himike12/OLED_Shoe/Hardware/Electronics/nRF52_Reference_Scematics/PCA10040-nRF52832 Bluetooth Smart,ANT,2.4GHz RF Development Board 1_1_1/Production files/GERBER/400150_PCB_Laminate_Specification.pdf

### PCB Laminate Specification

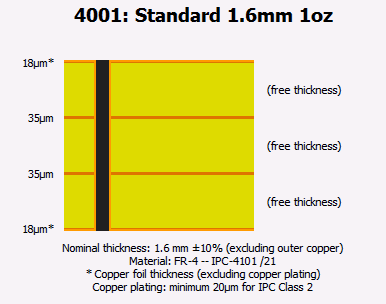
[picture p1: figure]

Page 1 of 1 | Rev. 1.0.0, 2016-03-10

PCB laminate parameters

PCB code | 4000150
Number of copper layers | 4 layers
Laminate material | FR4
Total board thickness | 1.6mm
PCB stackup | See Figure 1
Copper thickness | See Figure 1
Surface finish | Lead-Free HASL
Compliance with environmental directives | RoHS

Table 1: PCB substrate details

The PCB layer stackup order (from top layer and down) shall be as follows with reference to the Gerber file extensions given below:

- Top layer: | .GTL
- Mid layer 1: | .G1
- Mid layer 2: | .G2
- Bottom layer: | .GBL

Stackup

Figure 1: Elprint's standard 4 layer 4001 stackup
