himike12/OLED_Shoe/Hardware/BLE_module/BLE_Serial_Programs/BLE_Serial_Echo/BLE_Serial_Echo.ino

// Copyright (c) Sandeep Mistry. All rights reserved.
// Licensed under the MIT license. See LICENSE file in the project root for full license information.

/*
 * Serial Port over BLE
 * Create UART service compatible with Nordic's *nRF Toolbox* and Adafruit's *Bluefruit LE* iOS/Android apps.
 *
 * BLESerial class implements same protocols as Arduino's built-in Serial class and can be used as it's wireless
 * replacement. Data transfers are routed through a BLE service with TX and RX characteristics. To make the
 * service discoverable all UUIDs are NUS (Nordic UART Service) compatible.
 *
 * Please note that TX and RX characteristics use Notify and WriteWithoutResponse, so there's no guarantee
 * that the data will make it to the other end. However, under normal circumstances and reasonable signal
 * strengths everything works well.
 */


// Import libraries (BLEPeripheral depends on SPI)
#include <SPI.h>
#include <BLEPeripheral.h>
#include "BLESerial.h"

// define pins (varies per shield/board)
#define BLE_REQ   10
#define BLE_RDY   2
#define BLE_RST   9

// create ble serial instance, see pinouts above
BLESerial BLESerial(BLE_REQ, BLE_RDY, BLE_RST);

// LED status
bool LEDState = 0;

void LEDChange();

void setup() {
  // custom services and characteristics can be added as well
  BLESerial.setLocalName("UART");

  Serial.begin(9600);
  BLESerial.begin();

  pinMode(13, OUTPUT);
  digitalWrite(13, HIGH);       // sets the digital pin 13 on
  delay(1000);                  // waits for a second
  digitalWrite(13, LOW);        // sets the digital pin 13 off
}

void loop() {
  BLESerial.poll();

  forward();
  // loopback();
  // spam();
}


// forward received from Serial to BLESerial and vice versa
void forward() {
  if (BLESerial && Serial) {
    int byte;
    while ((byte = BLESerial.read()) > 0) {
      LEDChange(); // Change the state of the LED
      Serial.write((char)byte);
      BLESerial.write((char)byte);
    }
    while ((byte = Serial.read()) > 0) BLESerial.write((char)byte);
  }
}

// echo all received data back
void loopback() {
  if (BLESerial) {
    int byte;
    while ((byte = BLESerial.read()) > 0) BLESerial.write(byte);
  }
}

// periodically sent time stamps
void spam() {
  if (BLESerial) {
    BLESerial.print(millis());
    BLESerial.println(" tick-tacks!");
    delay(1000);
  }
}

// Change the state of the LED
void LEDChange() {
  if(LEDState == 1) {
    LEDState = 0;
    digitalWrite(13, LOW);
  }
  else {
    LEDState = 1;
    digitalWrite(13, HIGH);
  }
}
