himike12/OLED_Shoe/Hardware/BLE_module/Combine_Screen_and_BLE/recieve_data_and_display_modes/imageData.h

// Stores fixed images

#ifndef _IMAGE_DATA_H_
#define _IMAGE_DATA_H_

#include <Arduino.h>

#define SCREEN_HEIGHT 2886
      
//Stores the image
 // 'Gramophone', 312x74px  Brightness = 147
const unsigned char gramophoneLGray [] PROGMEM = {
 0xff, 0xff, 0xf3, 0xff, 0xff, 0xff, 0xff, 0xff, 0xff, 0xff, 0xff, 0xcf, 0xff, 0xff, 0xff, 0x80, 
  0x00, 0x00, 0x00, 0x01, 0xff, 0xff, 0xf8, 0x00, 0x00, 0x00, 0x00, 0x00, 0x00, 0x3f, 0xcc, 0x92, 
  0x00, 0x18, 0x00, 0x3f, 0xff, 0xff, 0xff, 0xff, 0xff, 0xf3, 0xff, 0xff, 0xff, 0xff, 0xff, 0xff, 
  0xff, 0xff, 0xcf, 0xff, 0xff, 0xff, 0x80, 0x00, 0x00, 0x00, 0x01, 0xff, 0xff, 0xf8, 0x00, 0x00, 
  0x00, 0x00, 0x00, 0x00, 0x7f, 0xf9, 0xc0, 0x00, 0x70, 0x00, 0x1f, 0xff, 0xff, 0xff, 0xff, 0xff, 
  0xf3, 0xff, 0xff, 0xff, 0xff, 0xff, 0xff, 0xff, 0xff, 0xcf, 0xff, 0xff, 0xff, 0x80, 0x00, 0x00, 
  0x00, 0x01, 0xff, 0xff, 0xfc, 0x00, 0x00, 0x00, 0x00, 0x00, 0x00, 0x7f, 0xf9, 0x98, 0x00, 0xe2, 
  0x00, 0x1f, 0xff, 0xff, 0xff, 0xff, 0xff, 0xf3, 0xff, 0xff, 0xff, 0xff, 0xff, 0xff, 0xff, 0xff, 
  0x8f, 0xff, 0xff, 0xff, 0x80, 0x00, 0x00, 0x00, 0x03, 0xff, 0xff, 0xfc, 0x00, 0x00, 0x00, 0x00, 
  0x00, 0x00, 0xff, 0xf3, 0xd8, 0x33, 0xc6, 0x00, 0x0f, 0xff, 0xff, 0xff, 0xff, 0xff, 0xe3, 0xff, 
  0xff, 0xff, 0xff, 0xff, 0xff, 0xff, 0xff, 0x9f, 0xff, 0xff, 0xff, 0xc0, 0x00, 0x00, 0x00, 0x03, 
  0xff, 0xff, 0xfc, 0x00, 0x00, 0x00, 0x00, 0x00, 0x00, 0xff, 0xff, 0xd8, 0xe7, 0x1f, 0x00, 0x07, 
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
  0x00, 0x00, 0x00, 0x00, 0x00, 0x00, 0x00, 0x00, 0x00, 0x00, 0x00, 0x00, 0x00, 0x00, 0x00, 0x00, 
  0x00, 0x00, 0x00, 0x00, 0x00, 0x00, 0x00, 0x00, 0x00, 0x00, 0x40, 0x00, 0x00, 0x00, 0x00, 0x00, 
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
};


#endif
