himike12/OLED_Shoe/Hardware/Teensy/Teensy_Screen_Demo/Teensy_Screen_Demo.ino

/* ****************************************************************************************
   Test program for displaying images on the Plastic Logic ePaper displays
**************************************************************************************** */
#include <Adafruit_GFX.h>
#include "PL_microEPD.h"

#define EPD_RST     A4      // Please align with your individual wiring
#define EPD_BUSY    A5      // Please align with your individual wiring
#define EPD_CS      10
PL_microEPD display(EPD_CS, EPD_RST, EPD_BUSY); 


 // 'Avatar1', 148x70px  Brightness = 147
const unsigned char gramophoneLGray [] PROGMEM = {
  0xff, 0xff, 0xff, 0xff, 0xff, 0xff, 0xff, 0xff, 0xff, 0xff, 0xff, 0xff, 0xff, 0xff, 0xff, 0xff, 
  0xf4, 0x00, 0x0f, 0xff, 0xff, 0xff, 0xff, 0xff, 0xff, 0xff, 0xff, 0xff, 0xff, 0xff, 0xff, 0xff, 
  0xff, 0xff, 0xff, 0xf8, 0x00, 0xff, 0xff, 0xff, 0xff, 0xff, 0xff, 0xff, 0xff, 0xff, 0xff, 0xff, 
  0xff, 0xff, 0xff, 0xff, 0xff, 0xff, 0xff, 0x0f, 0xff, 0xff, 0xff, 0xff, 0xff, 0xff, 0xff, 0xff, 
  0xff, 0xff, 0xff, 0xff, 0xff, 0xff, 0xff, 0xff, 0xff, 0xff, 0xff, 0xff, 0xff, 0xff, 0xff, 0xff, 
  0xff, 0xff, 0xff, 0xff, 0xff, 0xff, 0xff, 0xff, 0xff, 0xff, 0xff, 0xff, 0xff, 0xff, 0xff, 0xff, 
  0xff, 0xff, 0xff, 0xff, 0xff, 0xff, 0xff, 0xff, 0xff, 0xff, 0xff, 0xff, 0xff, 0xff, 0xff, 0xff, 
  0xff, 0xff, 0xff, 0xff, 0xff, 0xff, 0xff, 0xff, 0xff, 0xff, 0xff, 0xff, 0xff, 0xff, 0xff, 0xff, 
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
    display.drawBitmap(0, 0, myBitmap, 148, 70, EPD_LGRAY);
    //display.drawBitmap(0, 0, gramophoneDGray, 148, 70, EPD_DGRAY);
    //display.drawBitmap(0, 0, gramophoneBlack, 148, 70, EPD_BLACK);
    // Trigger a full image update
    display.update();
     
    
}

void loop() {

}
