himike12/OLED_Shoe/Hardware/ExampleCode/PlasticLogic_SD_Card_Contents/Reference Source Code/msp430/msp430-spi.c

/*
  Plastic Logic EPD project on MSP430

  Copyright (C) 2013 Plastic Logic Limited

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
  You should have received a copy of the GNU General Public License
  along with this program.  If not, see <http://www.gnu.org/licenses/>.
*/
/*
 * msp430-spi.c -- MSP430 SPI interface driver
 *
 * Authors: Nick Terry <nick.terry@plasticlogic.com>
 *
 */

#include <stdio.h>
#include <stdlib.h>

#include <msp430.h>

#include "types.h"
#include "assert.h"
#include "utils.h"

#include "msp430-defs.h"
#include "msp430-spi.h"
#include "msp430-gpio.h"

#define USCI_UNIT	A
#define USCI_CHAN	0
// Pin definitions for this unit
#define	SPI_SIMO		GPIO(3,4)
#define	SPI_SOMI		GPIO(3,5)
#define	SPI_CLK			GPIO(3,0)
#define SPI_CS GPIO(3,6)

#define SPI_MODE_0 (UCCKPH)                            /* CPOL=0 CPHA=0 */
#define SPI_MODE_1 (0)                         /* CPOL=0 CPHA=1 */
#define SPI_MODE_2 (UCCKPL | UCCKPH)    /* CPOL=1 CPHA=0 */
#define SPI_MODE_3 (UCCKPL)                            /* CPOL=1 CPHA=1 */
#define SPI_MODE_MASK (UCCKPL | UCCKPH)

/* We only support a single SPI bus and that bus is defined at compile
 * time.
 */
int spi_init(u8 spi_channel, u16 divisor)
{
	if (spi_channel != 0)
		return -EACCES;

	UCxnCTL1 |= UCSWRST;					// Put state machine in reset

	// Define chip select pins for multiple controllers
	gpio_request(SPI_SIMO,	PIN_SPECIAL | PIN_OUTPUT);
	gpio_request(SPI_SOMI, 	PIN_SPECIAL | PIN_INPUT);
	gpio_request(SPI_CLK, 	PIN_SPECIAL | PIN_OUTPUT);
	gpio_request(SPI_CS, PIN_GPIO | PIN_OUTPUT);
	//gpio_request(SPI_CS, PIN_GPIO | PIN_OUTPUT | PIN_INIT_HIGH);

	// SPI setting, MSb first, 8bit, Master Mode, 3 pin SPI, Synch Mode
	UCxnCTL0 |= (UCMST | UCSYNC | UCMSB | UCCKPH);

	UCxnCTL1 |= UCSSEL_2;					// SMCLK is selected
    UCxnBR0 = (divisor & 0x00ff);			// f_UCxCLK = 20MHz/1 = 20MHz
    UCxnBR1 = ((divisor >> 8) & 0x00ff);	//
	UCxnIE = 0x00;							// All interrupts disabled

	UCxnCTL1 &= ~UCSWRST;                  	// Release state machine from reset

	return 0;
}

void spi_close(void)
{
	UCxnCTL1 |= UCSWRST;                      // Put state machine in reset
}

u8 spi_write_read_byte(u8 byte)
{
    while (UCxnSTAT & UCBUSY) ;                     // Wait for all TX/RX to finish
    UCxnTXBUF = byte;                        // Write byte
    while (UCxnSTAT & UCBUSY) ;                     // Wait for all TX/RX to finish

    return UCxnRXBUF;                                      // Dummy read to empty RX buffer
}

/*
volatile u8 spi_write_read_byte(u8 byte) --> from Epson code, but not working
{
	unsigned int gie = __get_SR_register() & GIE;	// Store current GIE state

    __disable_interrupt();							// Make this operation atomic

    UCxnIFG &= ~UCRXIFG;							// Ensure RXIFG is clear

        while (!(UCxnIFG & UCTXIFG));				// Wait for TX buff empty
        UCxnTXBUF = 0xff;							// Write dummy byte to generate spi clock
        while (!(UCxnIFG & UCRXIFG));				// Wait for RX buffer (full)
        volatile u8 temp = UCxnRXBUF;						// store the byte

    __bis_SR_register(gie);                         // Restore original GIE state

    return temp;
}
*/

void spi_write_command(u8 command, u8 *params, int count)
{
	int i;

	gpio_set_value_lo(SPI_CS);
	command &= ~0x80;
	spi_write_read_byte(command);
	for (i=0; i<count; i++)
		spi_write_read_byte(*(params+i));
	gpio_set_value_hi(SPI_CS);
}

void spi_write_command_1param(u8 command, u8 param1)
{
	gpio_set_value_lo(SPI_CS);
	command &= ~0x80;
	spi_write_read_byte(command);
	spi_write_read_byte(param1);
	gpio_set_value_hi(SPI_CS);
}

void spi_write_command_2params(u8 command, u8 param1, u8 param2)
{
	gpio_set_value_lo(SPI_CS);
	command &= ~0x80;
	spi_write_read_byte(command);
	spi_write_read_byte(param1);
	spi_write_read_byte(param2);
	gpio_set_value_hi(SPI_CS);
}

void spi_write_command_3params(u8 command, u8 param1, u8 param2, u8 param3)
{
	gpio_set_value_lo(SPI_CS);
	command &= ~0x80;
	spi_write_read_byte(command);
	spi_write_read_byte(param1);
	spi_write_read_byte(param2);
	spi_write_read_byte(param3);
	gpio_set_value_hi(SPI_CS);
}

void spi_write_command_4params(u8 command, u8 param1, u8 param2, u8 param3, u8 param4)
{
	gpio_set_value_lo(SPI_CS);
	command &= ~0x80;
	spi_write_read_byte(command);
	spi_write_read_byte(param1);
	spi_write_read_byte(param2);
	spi_write_read_byte(param3);
	spi_write_read_byte(param4);
	gpio_set_value_hi(SPI_CS);
}

u8 spi_read_command_1param(u8 command)
{
	gpio_set_value_lo(SPI_CS);
	command |= 0x80;
	spi_write_read_byte(command);
	u8 temp = spi_write_read_byte(0x00);
	gpio_set_value_hi(SPI_CS);
	return temp;
}

u8* spi_read_command_2params(u8 command)
{
	static u8 return_value[2];
	gpio_set_value_lo(SPI_CS);
	command |= 0x80;
	spi_write_read_byte(command);
	return_value[0] = spi_write_read_byte(0x00);
	return_value[1] = spi_write_read_byte(0x00);
	gpio_set_value_hi(SPI_CS);
	return return_value;
}

void spi_read_command_2params1(u8 command, u8 *return_value)
{
	gpio_set_value_lo(SPI_CS);
	command |= 0x80;
	spi_write_read_byte(command);
	*return_value = spi_write_read_byte(0x00);
	*(return_value+1) = spi_write_read_byte(0x00);
	gpio_set_value_hi(SPI_CS);
}

int spi_read_command(u8 command, u8 *read_values_p, int count)
{
	int i;

	gpio_set_value_lo(SPI_CS);
	command |= 0x80;
	spi_write_read_byte(command);
	for (i=0; i<count; i++)
		*(read_values_p+i) = spi_write_read_byte(0x00);
	gpio_set_value_hi(SPI_CS);

	return i;
}

void print_spi_read_command(u8 command, int count)
{
	u8 *read_values_p;
	int i, ret;

	read_values_p = (u8*) malloc(count * sizeof(u8));
	if (read_values_p==0)
		abort_now("Fatal error in msp430-spi.c - print_spi_read_command: malloc not successful", ABORT_MISC);

	ret = spi_read_command(command, read_values_p, count);

	printf("Reg[%02xh] = ", command);
	for(i=0; i<ret; i++)
		printf("0x%02x ", *(read_values_p+i));
	printf("\n");

	free(read_values_p);
}

u8* spi_read_command_3params(u8 command)
{
	static u8 return_value[3];
	gpio_set_value_lo(SPI_CS);
	command |= 0x80;
	spi_write_read_byte(command);
	return_value[0] = spi_write_read_byte(0x00);
	return_value[1] = spi_write_read_byte(0x00);
	return_value[2] = spi_write_read_byte(0x00);
	gpio_set_value_hi(SPI_CS);
	return return_value;
}

u8* spi_read_command_4params(u8 command)
{
	static u8 return_value[4];
	gpio_set_value_lo(SPI_CS);
	command |= 0x80;
	spi_write_read_byte(command);
	return_value[0] = spi_write_read_byte(0x00);
	return_value[1] = spi_write_read_byte(0x00);
	return_value[2] = spi_write_read_byte(0x00);
	return_value[3] = spi_write_read_byte(0x00);
	gpio_set_value_hi(SPI_CS);
	return return_value;
}

u8 spi_read_command_1param_1dummy(u8 command)
{
	gpio_set_value_lo(SPI_CS);
	command |= 0x80;
	spi_write_read_byte(command);
	spi_write_read_byte(command); //dummy
	u8 temp = spi_write_read_byte(0x00);
	gpio_set_value_hi(SPI_CS);
	return temp;
}

void spi_write_command_and_bulk_data(u8 command, u8 *buffer, size_t size)
{
	gpio_set_value_lo(SPI_CS);
	command &= ~0x80;
	spi_write_read_byte(command);

    while (size--) {
    	spi_write_read_byte(*buffer);
    	buffer++;
    }
	gpio_set_value_hi(SPI_CS);
}

void spi_read_command_and_bulk_data(u8 command, u8 *buffer, size_t size)
{
	gpio_set_value_lo(SPI_CS);
	command |= 0x80;
	spi_write_read_byte(command);

    while (size--)
    {
    	*buffer = spi_write_read_byte(0x00); // 0x00 is dummy data
    	buffer++;
    }
	gpio_set_value_hi(SPI_CS);
}
/*
void spi_write_bulk_data(u8 *buffer, size_t size)
{
    while (size--) {
    	spi_write_byte(*buffer++, 1);
    }
}
*/

void spi_write_command_byte_repeat(u8 command, u8 data, size_t size)
{
	gpio_set_value_lo(SPI_CS);
	command &= ~0x80;
	spi_write_read_byte(command);

	while (size--) {
    	spi_write_read_byte(data);
    }
	gpio_set_value_hi(SPI_CS);
}
