himike12/OLED_Shoe/Hardware/ExampleCode/PlasticLogic_SD_Card_Contents/Reference Source Code/waveform.c

/*
 * waveform.h
 *
 *  Created on: 05.09.2014
 *      Author: andreas.meier
 */

#ifndef WAVEFORM_H_
#define WAVEFORM_H_

#include "waveform.h"
#include "types.h"
#include "UC8156.h"

u8 waveform_debug[WAVEFORM_LENGTH]= { \
0xAA, 0x6A, 0xAA, 0xAA, \
0x22, 0x22, 0x22, 0x22, \
0x00, 0x00, 0x00, 0x00, \
0x11, 0x11, 0x11, 0x11, \
0x11, 0x11, 0x11, 0x11, \
0x11, 0x11, 0x11, 0x11, \
0x11, 0x11, 0x11, 0x11, \
0x11, 0x11, 0x11, 0x11, \
0x11, 0x11, 0x11, 0x11, \
0x11, 0x11, 0x11, 0x11, \
0x11, 0x11, 0x11, 0x11, \
0x11, 0x11, 0x11, 0x11, \
0x11, 0x11, 0x11, 0x11, \
0x11, 0x11, 0x11, 0x11, \
0x11, 0x11, 0x11, 0x11, \
0x11, 0x11, 0x11, 0x11, \
0x11, 0x11, 0x11, 0x11, \
0x11, 0x11, 0x11, 0x11, \
0x11, 0x11, 0x11, 0x11, \
0x11, 0x11, 0x11, 0x11, \
0x11, 0x11, 0x11, 0x11, \
0x11, 0x11, 0x11, 0x11, \
0x11, 0x11, 0x11, 0x11, \
0x11, 0x11, 0x11, 0x11, \
0xF1, \
0x01, \
0x01, \
0x01, \
0x01, \
0x01, \
0x01, \
0x01, \
0x01, \
0x01, \
0x01, \
0x01, \
0x01, \
0x01, \
0x01, \
0x01, \
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
};

u8 waveform_long_null[WAVEFORM_LENGTH] = { \
                0xAA, 0xAA, 0xAA, 0xAA, \
                0xAA, 0xAA, 0xAA, 0xAA, \
                0xAA, 0xAA, 0xAA, 0xAA, \
                0xAA, 0xAA, 0xAA, 0xAA, \
                0xAA, 0xAA, 0xAA, 0xAA, \
                0xAA, 0xAA, 0xAA, 0xAA, \
                0xAA, 0xAA, 0xAA, 0xAA, \
                0xAA, 0xAA, 0xAA, 0xAA, \
                0xAA, 0xAA, 0xAA, 0xAA, \
                0xAA, 0xAA, 0xAA, 0xAA, \
                0xAA, 0xAA, 0xAA, 0xAA, \
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
0x00, 0x00, 0x00, 0x00,\
0x00, 0x00, 0x00, 0x00,\
0x00, 0x00, 0x00, 0x00,\
0x00, 0x00, 0x00, 0x00,\
0x00, 0x00, 0x00, 0x00,\
0x00, 0x00, 0x00, 0x00,\
0x00, 0x00, 0x00, 0x00,\
0x41,\
0x41,\
0x41,\
0x11,\
0x00,\
0x00,\
0x00,\
0x00,\
0x00,\
0x00,\
0x00,\
0x00,\
0x00,\
0x00,\
0x00,\
0x00,\
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
};

u8 waveform_S011_V1_0_VJW003_V2_T23_WfId3_uc8156_lut[] = { \
0x28, 0x6A, 0x6A, 0x69, \
0x28, 0xAA, 0x6A, 0x69, \
0x28, 0x2A, 0x68, 0x69, \
0x28, 0x2A, 0x29, 0x69, \
0x2A, 0x28, 0x29, 0xA9, \
0x29, 0x29, 0x29, 0x29, \
0xAA, 0xAA, 0xAA, 0xAA, \
0x00, 0x00, 0x00, 0x00, \
0x00, 0x00, 0x00, 0x00, \
0x00, 0x00, 0x00, 0x00, \
0x00, 0x00, 0x00, 0x00, \
0x00, 0x00, 0x00, 0x00, \
0x00, 0x00, 0x00, 0x00, \
0x00, 0x00, 0x00, 0x00, \
0x00, 0x00, 0x00, 0x00, \
0x00, 0x00, 0x00, 0x00, \
0x00, 0x00, 0x00, 0x00, \
0x00, 0x00, 0x00, 0x00, \
0x00, 0x00, 0x00, 0x00, \
0x00, 0x00, 0x00, 0x00, \
0x00, 0x00, 0x00, 0x00, \
0x00, 0x00, 0x00, 0x00, \
0x00, 0x00, 0x00, 0x00, \
0x00, 0x00, 0x00, 0x00, \
0x21, 0x11, 0x11, 0x11, \
0x11, 0x61, 0x21, 0x00, \
0x00, 0x00, 0x00, 0x00, \
0x00, 0x00, 0x00, 0x00, \
0x00, 0x00, 0x00, 0x00, \
0x00, 0x00, 0x00, 0x00, \
};

/*
 u8 waveform_MTP_array[] = { \
};
 */

#endif /* WAVEFORM_H_ */
