himike12/OLED_Shoe/Hardware/BLE_module/Screen_Test_Code/PL_GFXDemo_NewCustomLibVersion/PL_microEPD.h

/* *****************************************************************************************
PL_MICROEPD - A Universal Hardware Library for 1.1”, 1.4", 2.1" and 3.1" E-Paper displays 
(EPDs) from Plastic Logic based on UC8156 driver IC. The communication is SPI-based, for more
information about hook-up and tutorials please check: https://github.com/RobPo/Paperino.

Created by Robert Poser, Feb 9th 2018, Dresden/Germany. Released under BSD license
(3-clause BSD license), check license.md for more information.

We invested time and resources providing this open source code, please support Paperino and
open source hardware by purchasing this product @Crowd_supply @Watterott @Plasticlogic
***************************************************************************************** */
#ifndef PL_microEPD_h
#define PL_microEPD_h

#include <Adafruit_GFX.h>               //Only if Arduino attached
#ifdef ARDUINO
#include <SPI.h>
#elif defined(PLATFORM_ID)              //Only if a Particle attached
#include "Arduino.h"
#endif

#define EPD_WIDTH   (240)
#define EPD_HEIGHT  (146)

#define EPD_BLACK 0x00
#define EPD_DGRAY 0x01
#define EPD_LGRAY 0x02
#define EPD_WHITE 0x03

#define EPD_UPD_FULL  0x00            // Triggers a Full update, 4 GL, 800ms
#define EPD_UPD_PART  0x01            // Triggers a Partial update, 4 GL, 800ms
#define EPD_UPD_MONO  0x02            // Triggers a Partial Mono update, 2 GL, 250ms

#define EPD_TMG_LNG     880             // Duration{ms} of a full update
#define EPD_TMG_MID     340             // Duration{ms} of a partial update
#define EPD_TMG_SRT     1
#define EPD_TMG_SR2     70

#define EPD_REVISION          0x00  // Revision, Read only
#define EPD_PANELSETTING      0x01
#define EPD_DRIVERVOLTAGE     0x02
#define EPD_POWERCONTROL      0x03
#define EPD_TCOMTIMING        0x06
#define EPD_INTTEMPERATURE    0x07
#define EPD_SETRESOLUTION     0x0C
#define EPD_WRITEPXRECTSET    0x0D
#define EPD_PIXELACESSPOS     0x0E
#define EPD_DATENTRYMODE      0x0F
#define EPD_DISPLAYENGINE     0x14
#define EPD_VCOMCONFIG        0x18
#define EPD_BORDERSETTING     0x1D
#define EPD_POWERSEQUENCE     0x1F
#define EPD_SOFTWARERESET     0x20
#define EPD_PROGRAMMTP        0x40
#define EPD_MTPADDRESSSETTING 0x41
#define EPD_LOADMONOWF        0x44
#define EPD_REGREAD           0x80  // Instruction R/W bit set HIGH for data READ

#define ACC_GSEL    0x03    // Range: 0x03 - +/-2g, 0x05 - +/-4g, 0x08 - +/-8g, 0x0C - +/-16g
#define ACC_BW      0x0F    // Bandwidth: 0x08 = 7.81Hz bandwith, 0x0F = 1000Hz

class PL_microEPD : public Adafruit_GFX {

public:
    PL_microEPD(int8_t _cs, int8_t _rst=-1, int8_t _busy=-1);

    void begin(bool erase=true);
    void clear();
    void drawPixel(int16_t x, int16_t y, uint16_t color);
    void invert(void);
    void update(int updateMode=EPD_UPD_FULL);
    void setRotation(uint8_t o);
    void scrollText(String text, int cutout=24);
    void RSVPText(String text);
    void setVBorderColor(int color);
    uint8_t readTemperature(void);
    byte getEPDsize(void);
    void deepSleep(void);
    int width, height;
    char size[];

private:
    byte buffer[EPD_WIDTH * EPD_HEIGHT / 4];
    byte buffer2[EPD_WIDTH * EPD_HEIGHT / 4];
    int _EPDsize, _buffersize;
    int cs, rst, busy;
    int cursorX, cursorY;
    int fontHeight=8, fontWidth=5;
    int nextline=EPD_WIDTH/4;
    void waitForBusyInactive(int duration);
    void writeRegister(uint8_t address, int16_t val1, int16_t val2, int16_t val3, int16_t val4);
    byte readRegister(char address);
    int getPixel(int x, int y);
    void drawPixel2(int x, int y, int color);
    void scrambleBuffer(void);
    void writeBuffer(void);
    void WhiteErase(void);
    void powerOn(void);
    void powerOff(void);
};


class BO_BMA250 {

    public:
        BO_BMA250(uint8_t _cs2);
        void begin(void);
        void activateTapOnInt1(void);
        void clearLatchedInt1(void);
        void readAccel(void);
        void deepSuspend(void);

    private:
        int x, y, z, temp;
        int cs2;
};

#endif
