himike12/OLED_Shoe/Hardware/ExampleCode/PlasticLogic_SD_Card_Contents/Reference Source Code/msp430/msp430-sdcard.c

/*
  Plastic Logic EPD project on MSP430

  Copyright (C) 2013 Plastic Logic Limited

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
  You should have received a copy of the GNU General Public License
  along with this program.  If not, see <http://www.gnu.org/licenses/>.
*/
/*
 * msp430-sdcard.c -- MSP430 SD card SPI interface driver
 *
 * Authors: Nick Terry <nick.terry@plasticlogic.com>
 *
 */

#include "msp430.h"
#include "msp430-defs.h"
#include "types.h"
#include "msp430-gpio.h"
#include "msp430-sdcard.h"

#define CONFIG_PLAT_RUDDOCK2	1

#if CONFIG_PLAT_RUDDOCK2
#define USCI_UNIT	B
#define USCI_CHAN	0
// Pins from MSP430 connected to the SD Card
#define	SD_CS			GPIO(5,5)
#define	SD_SIMO			GPIO(3,1)
#define	SD_SOMI			GPIO(3,2)
#define	SD_CLK			GPIO(3,3)

#else

#endif

void SDCard_uDelay(u16 usecs)
{
	udelay(usecs);
}

void SDCard_init (void)
{
	UCxnCTL1 |= UCSWRST;                      	// Put state machine in reset

	gpio_request(SD_CS, 	PIN_GPIO    | PIN_OUTPUT | PIN_INIT_HIGH);
	gpio_request(SD_SIMO,	PIN_SPECIAL | PIN_OUTPUT);
	gpio_request(SD_SOMI, 	PIN_SPECIAL | PIN_INPUT);
	gpio_request(SD_CLK, 	PIN_SPECIAL | PIN_OUTPUT);

	// SPI Master, LSb first, 3pin SPI, Sync mode
	UCxnCTL0 |= (UCMST | UCSYNC | UCCKPL | UCMSB);

	UCxnCTL1 |= UCSSEL_2;                     	// Use SMCLK, keep RESET
    UCxnBR0 = 63;                           	// Initial SPI clock must be <400kHz
    UCxnBR1 = 0;                            	// f_UCxCLK = 20MHz/63 = 317kHz
	UCxnIE = 0x00;								// disable all interrupts
	UCxnCTL1 &= ~UCSWRST;                     	// **Release state machine from reset**
}

void SDCard_fastMode (void)
{
    UCxnCTL1 |= UCSWRST;                        // Put state machine in reset
    UCxnBR0 = 1;                                // f_UCxCLK = 20MHz/1 = 20MHz
    UCxnBR1 = 0;
    UCxnCTL1 &= ~UCSWRST;                       // Release USCI state machine
}

void SDCard_readFrame (u8 *pBuffer, u16 size)
{
    uint16_t gie = __get_SR_register() & GIE;   // Store current GIE state

    __disable_interrupt();                      // Make this operation atomic

    UCxnIFG &= ~UCRXIFG;                        // Ensure RXIFG is clear

    // Clock the actual data transfer and receive the bytes
    while (size--){
        while (!(UCxnIFG & UCTXIFG)) ;          // Wait while not ready for TX
        UCxnTXBUF = 0xff;                       // Write dummy byte
        while (!(UCxnIFG & UCRXIFG)) ;          // Wait for RX buffer (full)
        *pBuffer++ = UCxnRXBUF;
    }

    __bis_SR_register(gie);                     // Restore original GIE state
}

void SDCard_sendFrame (u8 *pBuffer, u16 size)
{
    uint16_t gie = __get_SR_register() & GIE;   // Store current GIE state

    __disable_interrupt();                      // Make this operation atomic

    // Clock the actual data transfer and send the bytes. Note that we
    // intentionally not read out the receive buffer during frame transmission
    // in order to optimize transfer speed, however we need to take care of the
    // resulting overrun condition.
    while (size--){
        while (!(UCxnIFG & UCTXIFG)) ;          // Wait while not ready for TX
        UCxnTXBUF = *pBuffer++;                 // Write byte
    }
    while (UCxnSTAT & UCBUSY) ;                 // Wait for all TX/RX to finish

    UCxnRXBUF;                                  // Dummy read to empty RX buffer
                                                // and clear any overrun conditions

    __bis_SR_register(gie);                     // Restore original GIE state
}

void SDCard_setCSHigh (void)
{
	gpio_set_value_hi(SD_CS);
}

void SDCard_setCSLow (void)
{
	gpio_set_value_lo(SD_CS);
}
