himike12/OLED_Shoe/Hardware/ExampleCode/PlasticLogic_SD_Card_Contents/Reference Source Code/msp430/msp430-timers.c

/*
  Plastic Logic EPD project on MSP430

  Copyright (C) 2013 Plastic Logic Limited

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
  You should have received a copy of the GNU General Public License
  along with this program.  If not, see <http://www.gnu.org/licenses/>.
*/
/*
 * msp430-timers.c -- MSP430 timer functions
 *
 * Authors: Nick Terry <nick.terry@plasticlogic.com>
 *
 */

#include <msp430.h>
#include "types.h"
#include "msp430-gpio.h"

#define INIT_COUNT_L 0xC3
#define INIT_COUNT_H 0x50

static int delay;

#define CPU_CYCLES_PER_USECOND (CPU_CLOCK_SPEED_IN_HZ/1000000L)
#define CPU_CYCLES_PER_MSECOND (CPU_CLOCK_SPEED_IN_HZ/1000L)

/* Functions for delay/sleep. Needs to be calibrated */
void udelay(u16 us)
{
	while (us--)
	{
		__delay_cycles(CPU_CYCLES_PER_USECOND);
	}
}

void mdelay(u16 ms)
{
    while (ms--)
    {
        __delay_cycles(CPU_CYCLES_PER_MSECOND);
    }
}

void msleep(u16 ms)
{
	mdelay(ms);
}


void init_rtc()
{
	  // Setup RTC Timer
	  RTCCTL01 |= RTCTEVIE;		// interrupt enable
	  RTCCTL01 &= ~RTCMODE; 	// counter mode
	  RTCCTL01 |= RTCSSEL_0;
	  RTCCTL01 |= RTCTEV_1;

	  // load the counter for a 10s timeout
	  RTCNT1 = 0xFF - INIT_COUNT_H;
	  RTCNT2 = 0xFF - INIT_COUNT_L;

	  RTCCTL01 &= ~RTCHOLD; 	// start counter
}

#pragma vector=RTC_VECTOR
__interrupt void RTC_ISR(void)
{
	unsigned int gie = __get_SR_register();

	LPM3_EXIT;

    __disable_interrupt();

    switch(__even_in_range(RTCIV,16))
    {
		case 0: break;            		// No interrupts
		case 2: break;            		// RTCRDYIFG
		case 4: break;             		// RTCEVIFG => timer interrupt
		case 6: break;                  // RTCAIFG
		case 8: break;                  // RT0PSIFG
		case 10: break;                 // RT1PSIFG
		case 12: break;                 // Reserved
		case 14: break;                 // Reserved
		case 16: break;                 // Reserved
		default: break;
    }

    __bis_SR_register(gie);
}

void timer_start(void)
{
	delay = 1;
	TA0CTL = TASSEL_1 | ID_3 | MC_2 | TACLR | TAIE;         // ACK ( = 10kHz), contmode, clear interrupt enable
	TA0R = 0xFFFF - 0x927C;									// Configure the timer
}

void timer_stop(void)
{
	TA0CTL = MC_0;
}

#pragma vector = TIMER0_A1_VECTOR
__interrupt void TIMER0_ISR(void)
{
	unsigned int gie = __get_SR_register();

	__disable_interrupt();

	switch(__even_in_range(TA0IV,16))
	{
	case 0x0E:
		delay--;
		if(delay < 0)
		{
			timer_stop();
			timer_start();
		}

		// reload the timer for 1 minute
		TA0R = 0xFFFF - 0x927C;

		break;
	default:break;

	}

    __bis_SR_register(gie);
}
