himike12/OLED_Shoe/Hardware/ExampleCode/PlasticLogic_SD_Card_Contents/Reference Source Code/utils.c

/*
  Plastic Logic EPD project on MSP430

  Copyright (C) 2013 Plastic Logic Limited

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
  You should have received a copy of the GNU General Public License
  along with this program.  If not, see <http://www.gnu.org/licenses/>.
*/
/*
 * utils.c -- random homeless functions
 *
 * Authors: Nick Terry <nick.terry@plasticlogic.com>
 *          Guillaume Tucker <guillaume.tucker@plasticlogic.com>
 *
 */

#include <stdlib.h>
#include <stdio.h>
#include "types.h"
#include "FatFs/ff.h"
#include "msp430-gpio.h"
#include "pnm-utils.h"
#include "utils.h"

u16 __bswap_16(u16 x)
{
	return _swap_bytes(x);
}

u32 __bswap_32(u32 x)
{
	param32 tmp;

	tmp.data32 = x;
	//u16 tmp_msw = __bswap_16(tmp.msw);
	//tmp.msw = __bswap_16(tmp.lsw);
	//tmp.lsw = tmp_msw;
	return tmp.data32;
}

void util_id_pins(short *gpio, int pin_count)
{
	int pin;
	int clk;

	for (pin = 0; pin < pin_count; pin++)
	{
		gpio_request(gpio[pin], PIN_GPIO | PIN_OUTPUT | PIN_INIT_LOW);
	}

	while (1) {
		for (pin = 0; pin < pin_count; pin++)
		{
			for (clk = 0; clk <= pin; clk++) {
				gpio_set_value_hi(gpio[pin]);
				gpio_set_value_lo(gpio[pin]);
			}
		}
	}
}

/* ----------------------------------------------------------------------------
 * Lightweight string parser
 */

int parser_find_str(const char *str, const char *sep, int skip)
{
	int i;

	for (i = 0; str[i]; ++i) {
		int found = 0;
		int j;

		for (j = 0; sep[j]; ++j) {
			if (str[i] == sep[j]) {
				found = 1;
				break;
			}
		}

		if (found ^ skip)
			return i;
	}

	return -1;
}

int parser_read_str(const char *str, const char *sep, char *out, int out_len)
{
	int len;

	len = parser_find_str(str, sep, 0);

	if (!len)
		return 0;

	if (len == -1)
		while (str[++len]);

	if (len >= out_len)
		return -1;

	memcpy(out, str, len);
	out[len] = '\0';
	len += parser_find_str((str + len), sep, 1);

	return len;
}

int parser_read_int(const char *str, const char *sep, int *out)
{
	char value[16];
	const int len = parser_read_str(str, sep, value, sizeof(value));

	if (len >= 0)
		*out = atoi(value);

	return len;
}

int parser_read_int_list(const char *str, const char *sep, int **list)
{
	const char *opt = str;

	while (*list != NULL) {
		const int len = parser_read_int(opt, sep, *list++);

		if (len <= 0)
			return len;

		opt += len;
	}

	return (opt - str);
}

int parser_read_area(const char *str, const char *sep, struct area *a)
{
	//int *coords[] = { &a->left, &a->top, &a->width, &a->height, NULL };

	//return parser_read_int_list(str, sep, coords);
	return 0;
}

int parser_read_file_line(FIL *f, char *buffer, int max_length)
{
	size_t count;
	char *out;
	int i;

	for (i = 0, out = buffer; i < max_length; ++i, ++out) {
		if (f_read(f, out, 1, &count) != FR_OK)
			return -1;

		if ((*out == '\n') || !count)
			break;

		if (*out == '\r')
			--out;
	}

	if (i == max_length)
		return -1;

	*out = '\0';

	return !!count;
}

/* ----------------------------------------------------------------------------
 * Debug utilities
 */

void dump_hex(const void *data, uint16_t len)
{
	static const char hex[16] = {
		'0', '1', '2', '3', '4', '5', '6', '7',
		'8', '9', 'A', 'B', 'C', 'D', 'E', 'F'
	};
	char s[] = "[XXXX] XX XX XX XX XX XX XX XX XX XX XX XX XX XX XX XX";
	char *cur;
	uint16_t i;

	if (!len)
		return;

	for (i = 0, cur = s; i < len; ++i) {
		const uint8_t byte = ((const uint8_t *)data)[i];

		if (!(i & 0xF)) {
			uint16_t addr = i;
			uint16_t j;

			if (i)
				puts(s);

			cur = s + 4;

			for (j = 4; j; --j) {
				*cur-- = hex[addr & 0xF];
				addr >>= 4;
			}

			cur = s + 7;
		}

		*cur++ = hex[byte >> 4];
		*cur++ = hex[byte & 0xF];
		++cur;
	}

	i %= 16;

	if (i) {
		cur = s + 6 + (i * 3);
		*cur++ = '\n';
		*cur++ = '\0';
	}

	puts(s);
}

/*Converts image data to 2 bit per pixel data */
void pack_2bpp(u8 *in, u8 *out, int in_count)
{
	while (in_count > 0) {
		*out = (u8)(((in[0] >> 6) << 6) | ((in[1] >> 6) << 4) | ((in[2] >> 6) << 2) | (in[3] >> 6));
		in += 4;
		out++;
		in_count -= 4;
	}
}

void abort_now(const char *error_string, enum led_error_code error_code)
{
	printf(error_string);
	printf("\n\n");

	for (;;)
	{
		int i;
		mdelay(1500);
		for (i = 0; i < error_code; i++)
		{
			gpio_set_value_hi(PIN_ERROR_LED);
			mdelay(250);
			gpio_set_value_lo(PIN_ERROR_LED);
			mdelay(250);
		}
	}

	exit(EXIT_FAILURE);
}

int join_path(char *path, size_t n, const char *dir, const char *file)
{
	return (snprintf(path, n, "%s/%s", dir, file) >= n) ? -1 : 0;
}
