himike12/OLED_Shoe/Hardware/ExampleCode/PlasticLogic_SD_Card_Contents/Reference Source Code/config_display_type.h

/*
 * config_display_type.h
 *
 *  Created on: 9 Sep 2016
 *      Author: andreas.meier
 */

#ifndef CONFIG_DISPLAY_TYPE_H_
#define CONFIG_DISPLAY_TYPE_H_

enum DISPLAY_TYPE {S014_T1_1, S021_T1_1, S031_T1_1, S011_T1_1, UNKNOWN};

void set_display_type(int display_type);

#endif /* CONFIG_DISPLAY_TYPE_H_ */
