himike12/OLED_Shoe/Hardware/ExampleCode/PlasticLogic_SD_Card_Contents/Reference Source Code/verification_functions.h

/*
 * verification_functions.h
 *
 *  Created on: 13.11.2014
 *      Author: andreas.meier
 */

#ifndef VERIFICATION_FUNCTIONS_H_
#define VERIFICATION_FUNCTIONS_H_

#include "types.h"

void check_temperature_sensor();
u8* read_waveform_LUT();
void read_and_print_MTP();
void send_drift_test_image();

#endif /* VERIFICATION_FUNCTIONS_H_ */
