himike12/OLED_Shoe/Hardware/ExampleCode/PlasticLogic_SD_Card_Contents/Reference Source Code/waveform.h

/*
 * waveform.h
 *
 *  Created on: 13.11.2014
 *      Author: andreas.meier
 */

#ifndef WAVEFORM_H_
#define WAVEFORM_H_

extern u8 waveform_default[];
extern u8 waveform_debug[];
extern u8 waveform_long_null[];
extern u8 waveform_test[];
extern u8 waveform_S031_V7D035_2GL_V1_23_0[];
extern u8 waveform_S011_V1_0_VJW003_V2_T23_WfId3_uc8156_lut[];
//extern u8 waveform_MTP_array[];

#endif /* WAVEFORM_H_ */
